apurse/ReSpace-copy/Arduino/Swarm-Behaviour-Scripts/swarm-receiving/swarm-receiving.ino

#include <Guppy.h>

Guppy guppy;

uint8_t address[6] = "00001";

void setup() {
  Serial.begin(9600);
  guppy.begin();
  guppy.initRadio();
  guppy.startListening(address);
}

void loop() {
  String message = "";
  message = guppy.receive();
  // wait for message
  if (message != "") {
    Serial.println(message);
  }
  
  if (message == "light_on")
  {
    guppy.lightOn();
  }
  else if (message == "light_off")
  {
    guppy.lightOff();
  }
}
